Jeremy-Surgeon/TACTRACE-Trainer/hardware/kicad/TacTrace_V1_4_Full.kicad_sch

## KiCad design hardware/kicad/TacTrace_V1_4_Full.kicad_sch (2026-05-02)

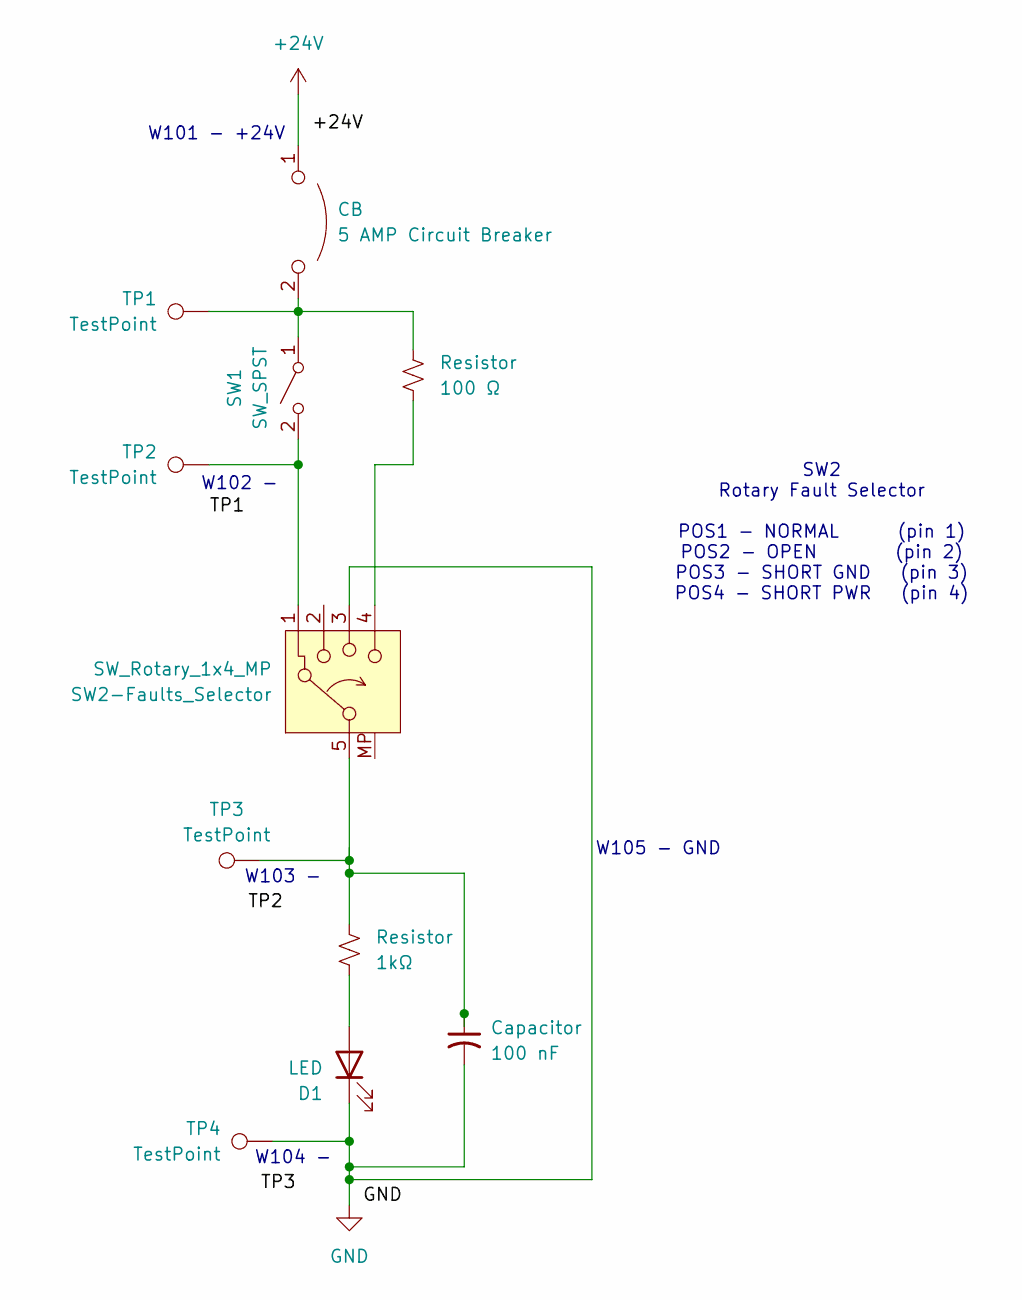
[picture p18: schematic TacTrace_V1_4_Full.kicad_sch]

Parts:
CB: 5 AMP Circuit Breaker
Capacitor: 100 nF
D1: LED
Resistor: 100 Ω
SW1: SW_SPST
SW2-Faults_Selector: SW_Rotary_1x4_MP
TP1, TP2, TP3, TP4: TestPoint

Connections:
+24V: CB.1
GND: Capacitor.2, D1.1 (K), SW2-Faults_Selector.3, TP4.1
unnamed: CB.2, Resistor.2, SW1.1 (A), TP1.1
unnamed: Capacitor.1, Resistor.2, SW2-Faults_Selector.5, TP3.1
unnamed: D1.2 (A), Resistor.1
unnamed: Resistor.1, SW2-Faults_Selector.4
unnamed: SW1.2 (B), SW2-Faults_Selector.1, TP2.1

Notes on the sheet:
W104 -
W102 -
SW2 Rotary Fault Selector POS1 - NORMAL (pin 1) POS2 - OPEN (pin 2) POS3 - SHORT GND (pin 3) POS4 - SHORT PWR (pin 4)
W105 - GND
W101 - +24V
W103 -
