Jeremy-Surgeon/TACTRACE-Trainer/hardware/kicad/TacTrace_V1_4_Simple.kicad_sch

## KiCad design hardware/kicad/TacTrace_V1_4_Simple.kicad_sch (2026-05-02)

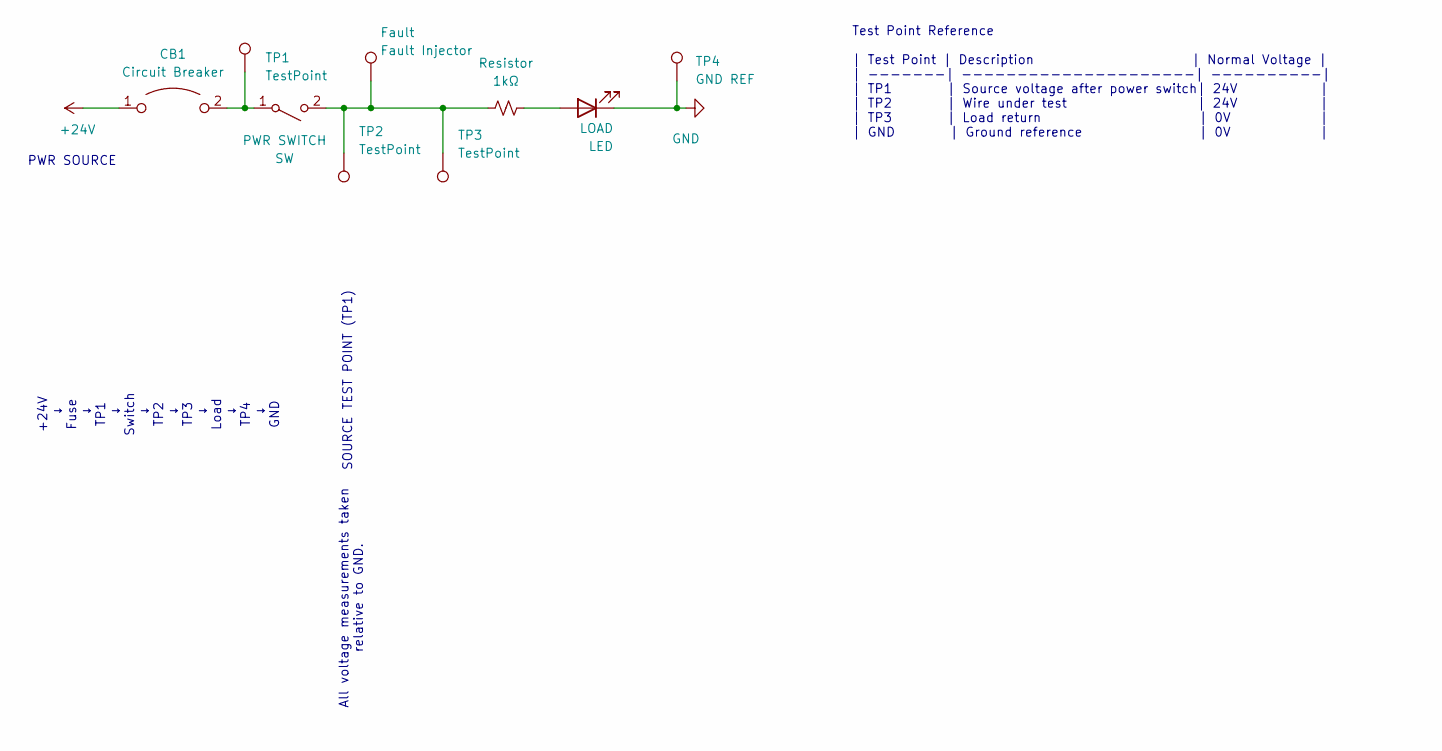
[picture p19: schematic TacTrace_V1_4_Simple.kicad_sch]

Parts:
CB1: Circuit Breaker
Fault: Fault Injector
LED: LOAD
Resistor: 1kΩ
SW: PWR SWITCH
TP1, TP2, TP3: TestPoint
TP4: GND REF

Connections:
+24V: CB1.1
GND: LED.1 (K), TP4.1
unnamed: CB1.2, SW.1 (A), TP1.1
unnamed: Fault.1, Resistor.1, SW.2 (B), TP2.1, TP3.1
unnamed: LED.2 (A), Resistor.2

Notes on the sheet:
All voltage measurements taken relative to GND.
Test Point Reference | Test Point | Description | Normal Voltage | | -------| ---------------------| ----------| | TP1 | Source voltage after power switch| 24V | | TP2 | Wire under test | 24V | | TP3 | Load return | 0V | | GND | Ground reference | 0V |
PWR SOURCE
SOURCE TEST POINT (TP1)
+24V ↓ Fuse ↓ TP1 ↓ Switch ↓ TP2 ↓ TP3 ↓ Load ↓ TP4 ↓ GND
